e1kable/two-axis-rotation-table/include/sloping.h

#ifndef ROT_TABLE_SLOPING_H
#define ROT_TABLE_SLOPING_H

using namespace std;

float linearSlope(float phi_i, float ts, float phiDotMax, float phi);
uint32_t generateSlopeSteps(steps_t i, float phi, float phiDotMax, steps_t totalSteps, steps_t &Nsteps);

#endif
